Wykerd/modular-gps-tracker/Joernaal/21 April 2018.docx

21 April 2018

I visited Dr. Danie Ludick, who works at Stellenbosch University today to get expert advice on what capacitors and resistors to order. I also wanted him to check my design to confirm that it will work. He said that the design looks promising and that I should let it get manufactured, if it is to not work, he can help me solve the problem. He also said that he would send my design to his colleagues to also confirm that it will work. He also told me should I need help I can visit the University as they have all the tools I would need to make my PCB.

Below is a screenshot of the email I sent him:

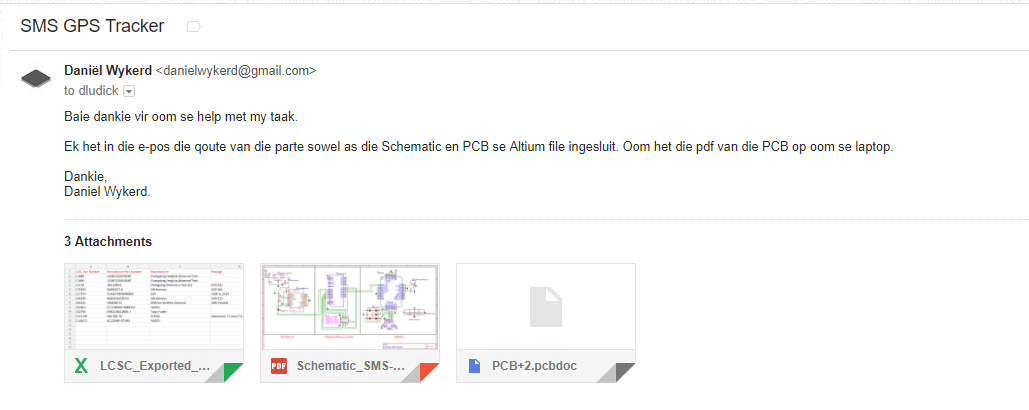
[picture p13: figure]
