Wykerd/modular-gps-tracker/Joernaal/28 april.docx

28 april

Started writing the research plan.

29 april

Made a case.

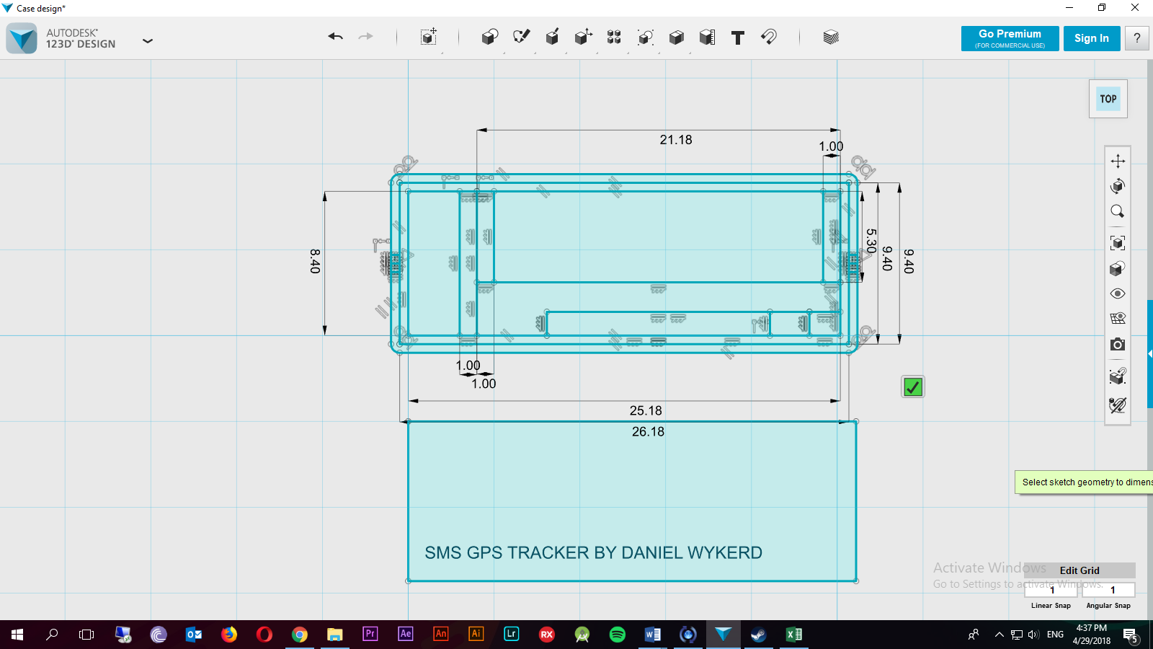
[picture p14: figure]
