Wykerd/modular-gps-tracker/Screenshots van code.docx

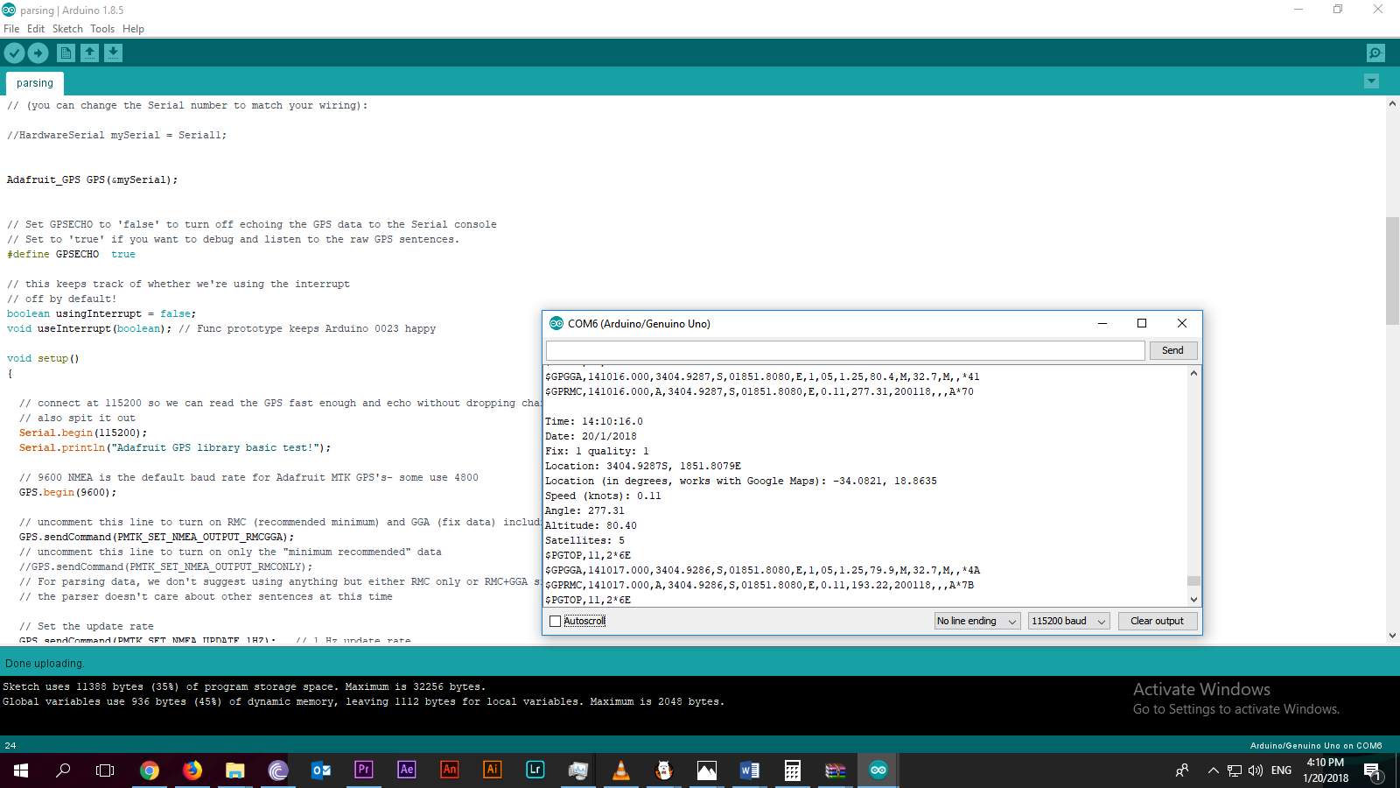
[picture p42: figure]

GPS test

1/20/2018
