Wykerd/modular-gps-tracker/Joernaal/22 April 2018.docx

22 April 2018

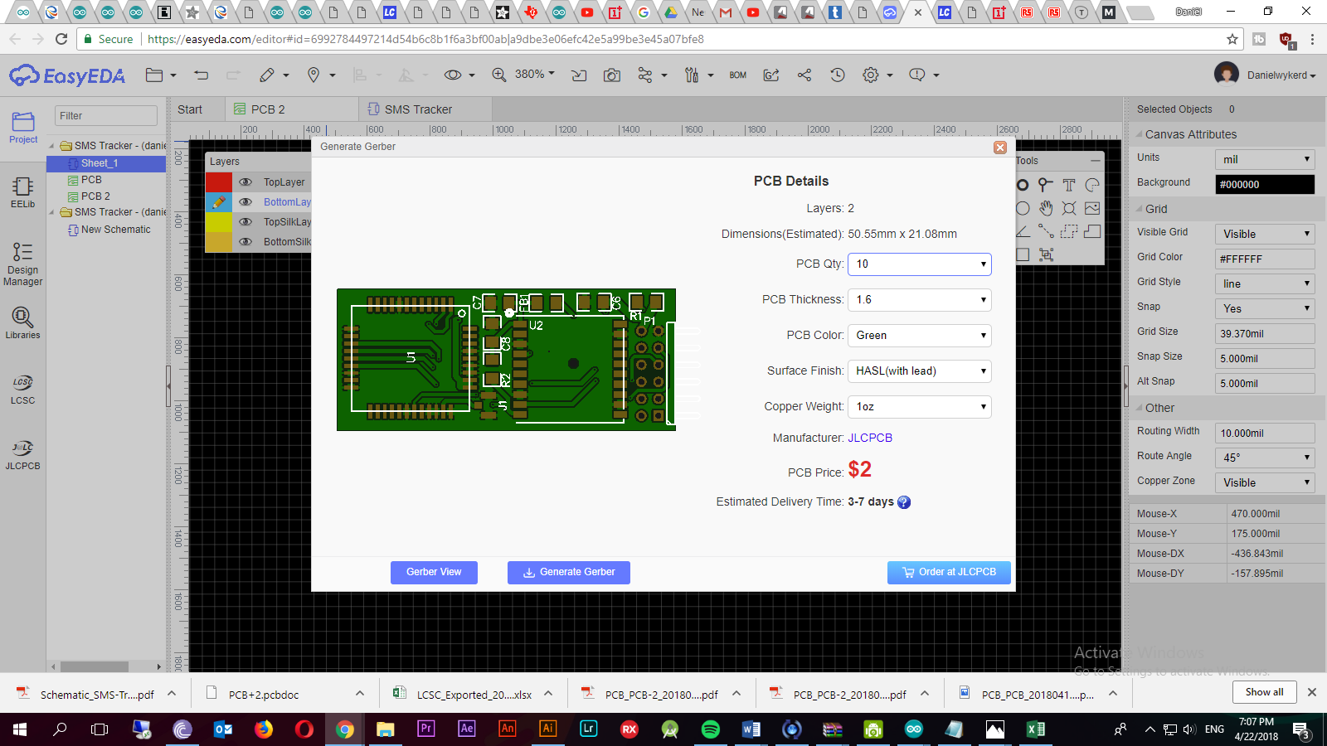
[picture p43: figure]
