Wykerd/modular-gps-tracker/Case bare.PNG

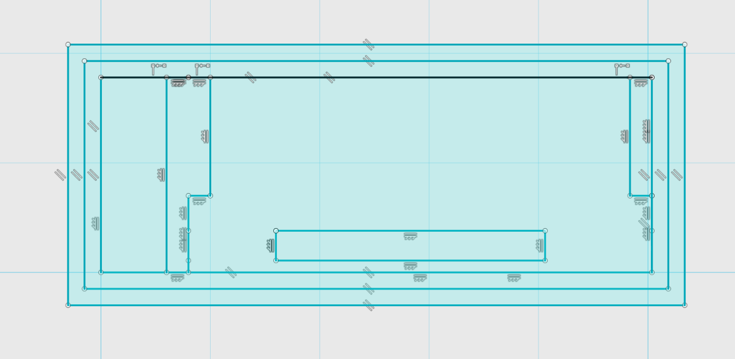
Case bare.PNG
