Wykerd/modular-gps-tracker/casedimensions.PNG

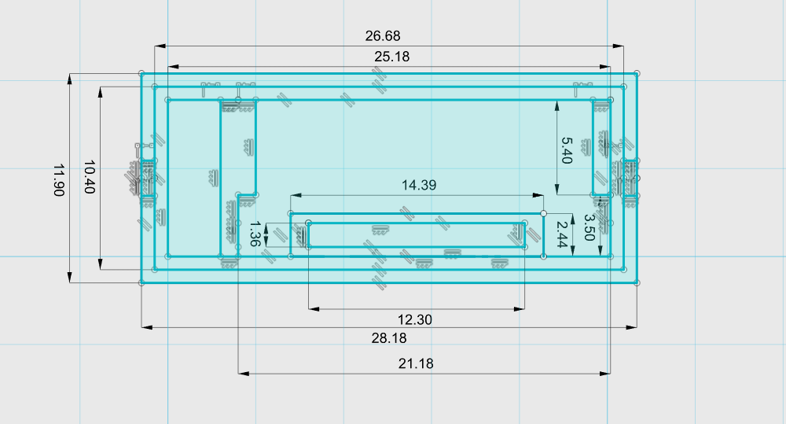
casedimensions.PNG
