Wykerd/modular-gps-tracker/Images/Hardware/20180120_152852.jpg

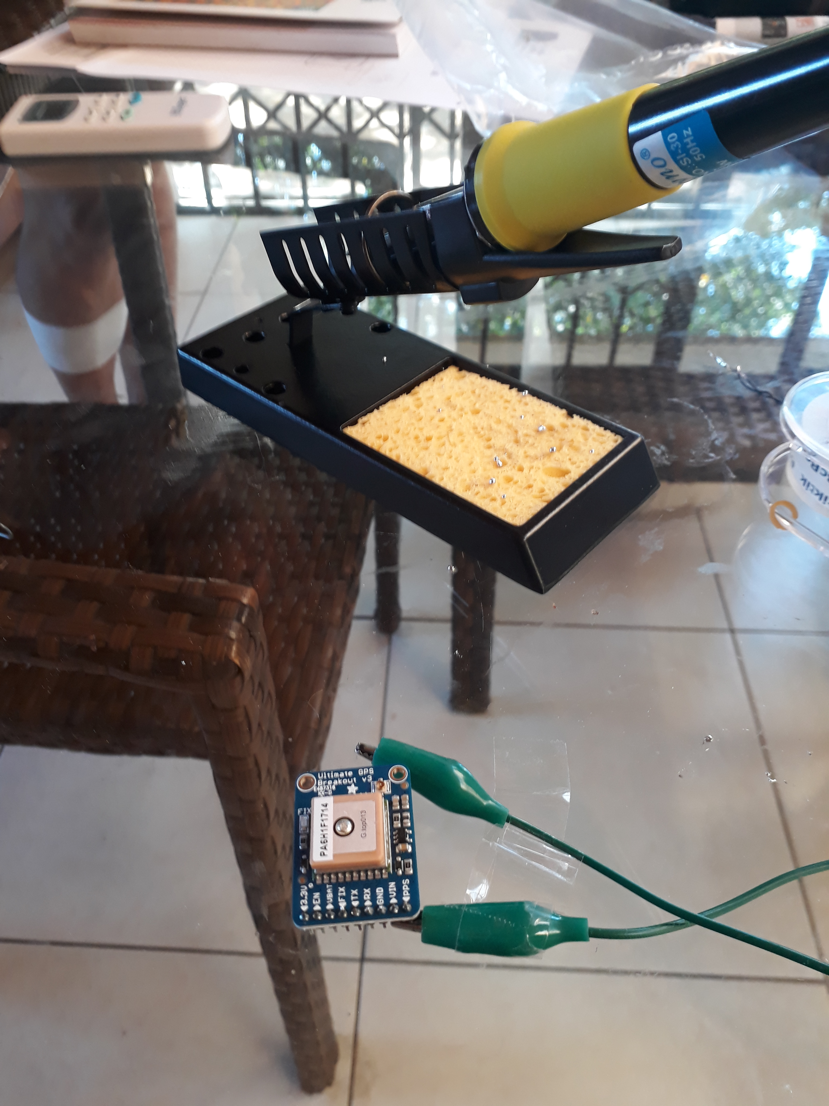
Images/Hardware/20180120_152852.jpg
