Wykerd/modular-gps-tracker/Images/Hardware/20180120_152857.jpg

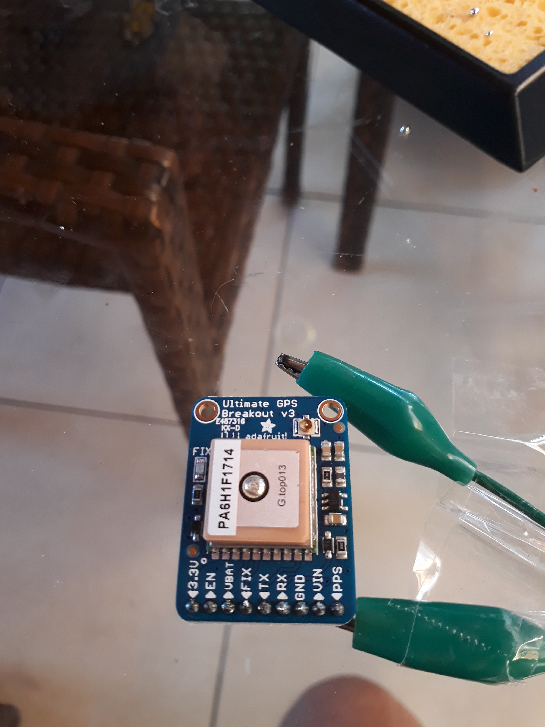
Images/Hardware/20180120_152857.jpg
