Wykerd/modular-gps-tracker/Images/Hardware/20180120_152902.jpg

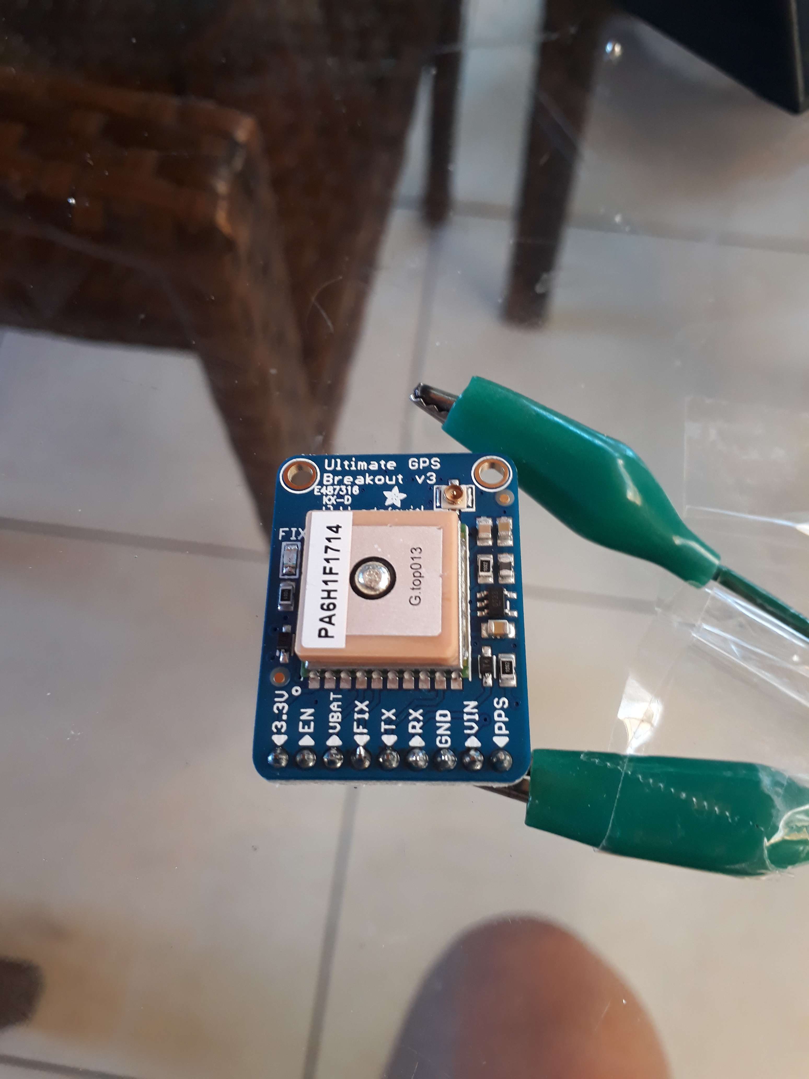
Images/Hardware/20180120_152902.jpg
