Wykerd/modular-gps-tracker/Images/Hardware/20180120_161100.jpg

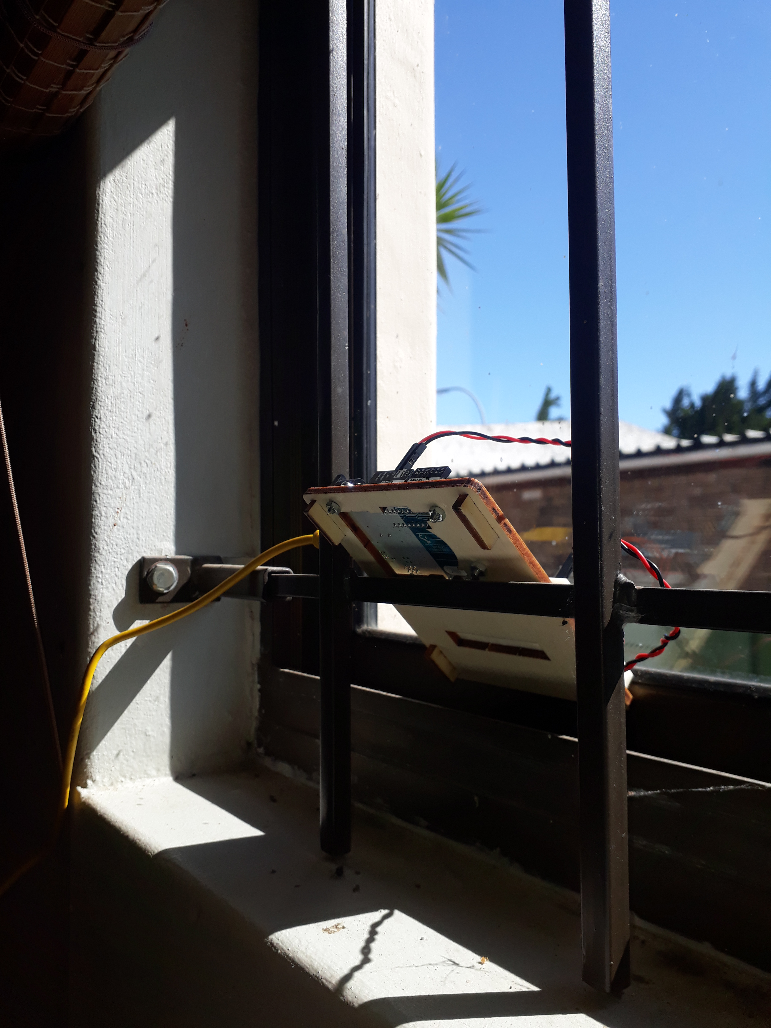
Images/Hardware/20180120_161100.jpg
