Wykerd/modular-gps-tracker/Images/Hardware/20180120_161110.jpg

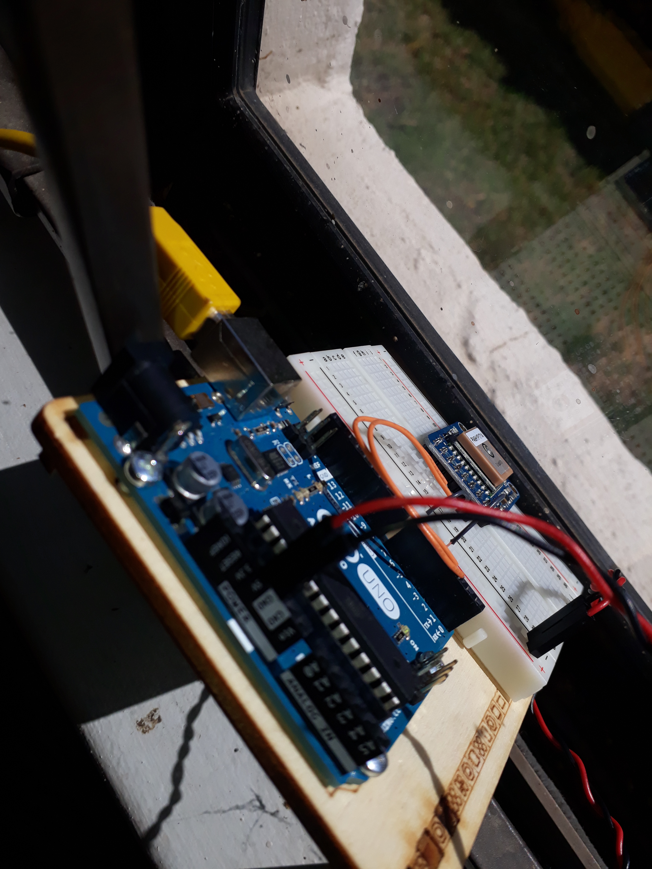
Images/Hardware/20180120_161110.jpg
