Wykerd/modular-gps-tracker/Images/Hardware/20180120_161119.jpg

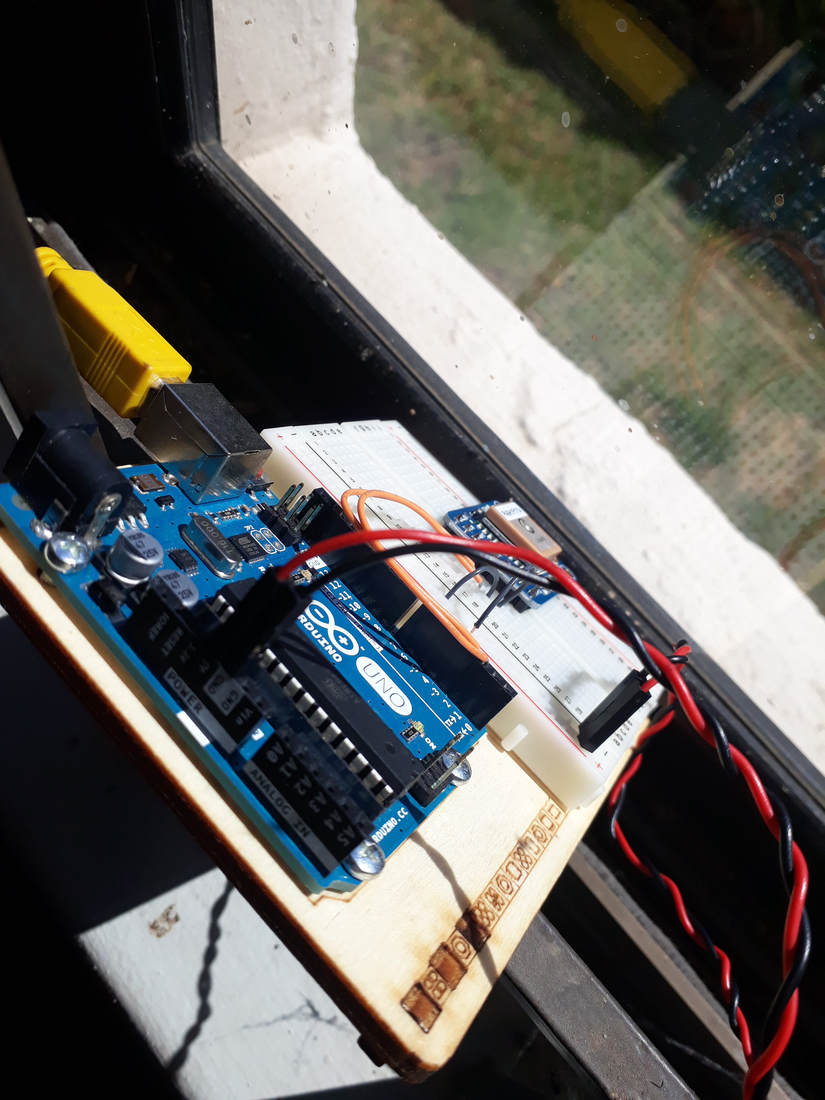
Images/Hardware/20180120_161119.jpg
