Wykerd/modular-gps-tracker/Images/Hardware/20180121_085342.jpg

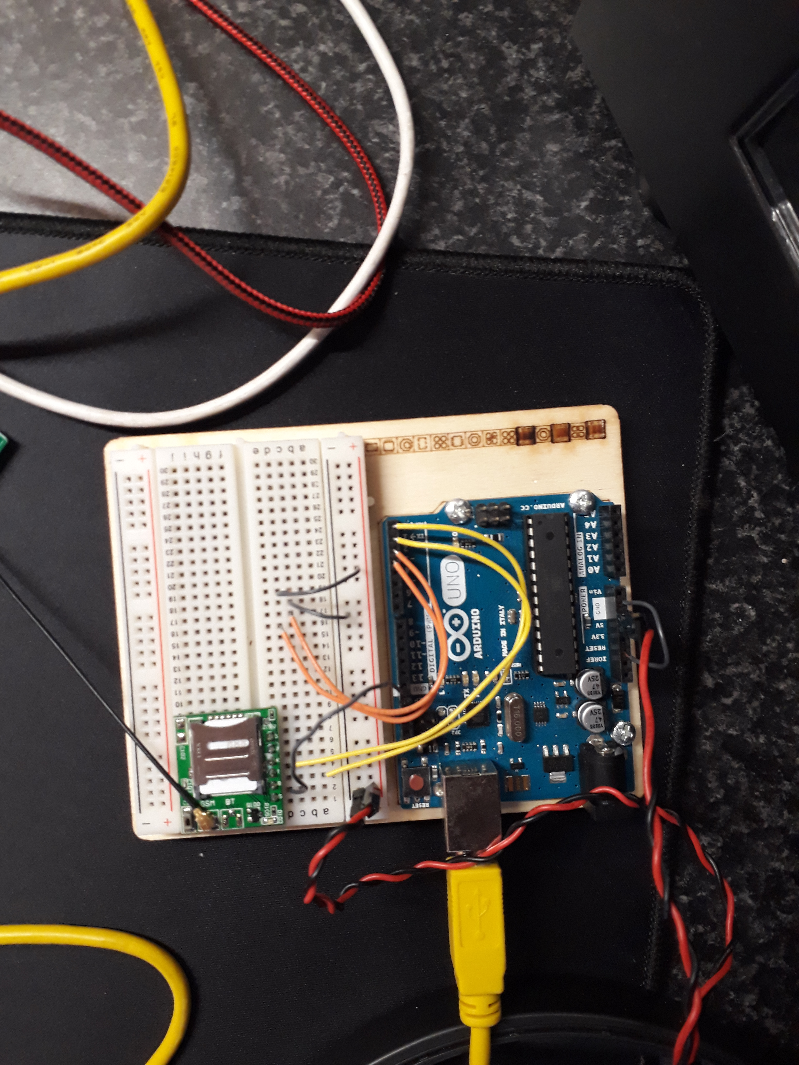
Images/Hardware/20180121_085342.jpg
