Wykerd/modular-gps-tracker/Images/Hardware/20180121_085343(0).jpg

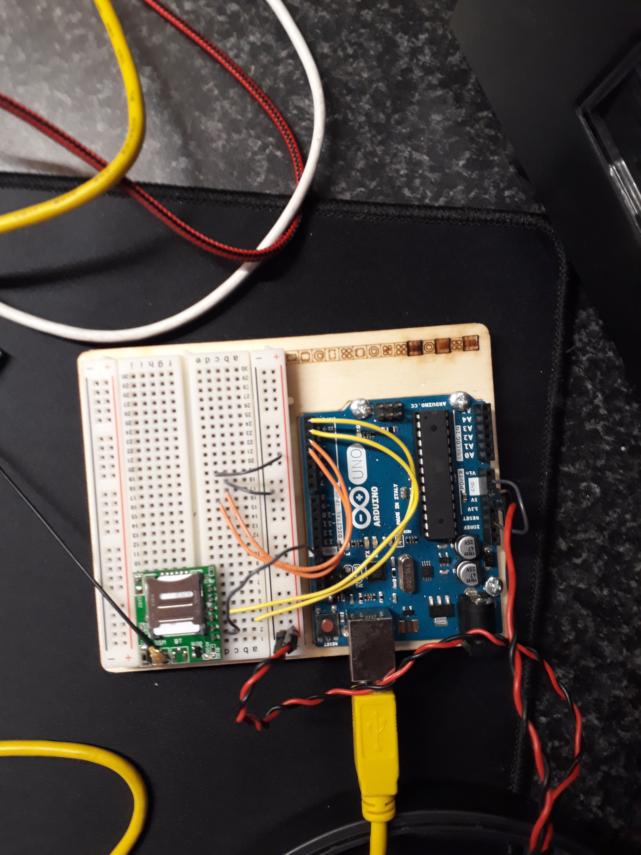
Images/Hardware/20180121_085343(0).jpg
