Wykerd/modular-gps-tracker/Images/Hardware/20180122_201225.jpg

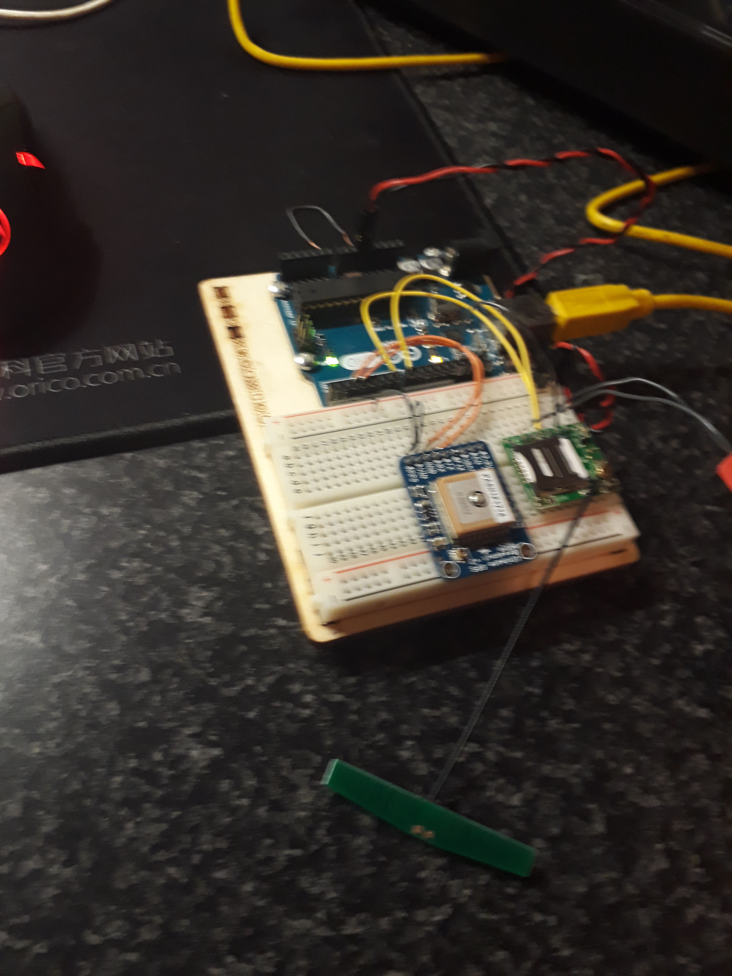
Images/Hardware/20180122_201225.jpg
