Wykerd/modular-gps-tracker/Images/Hardware/20180122_201243.jpg

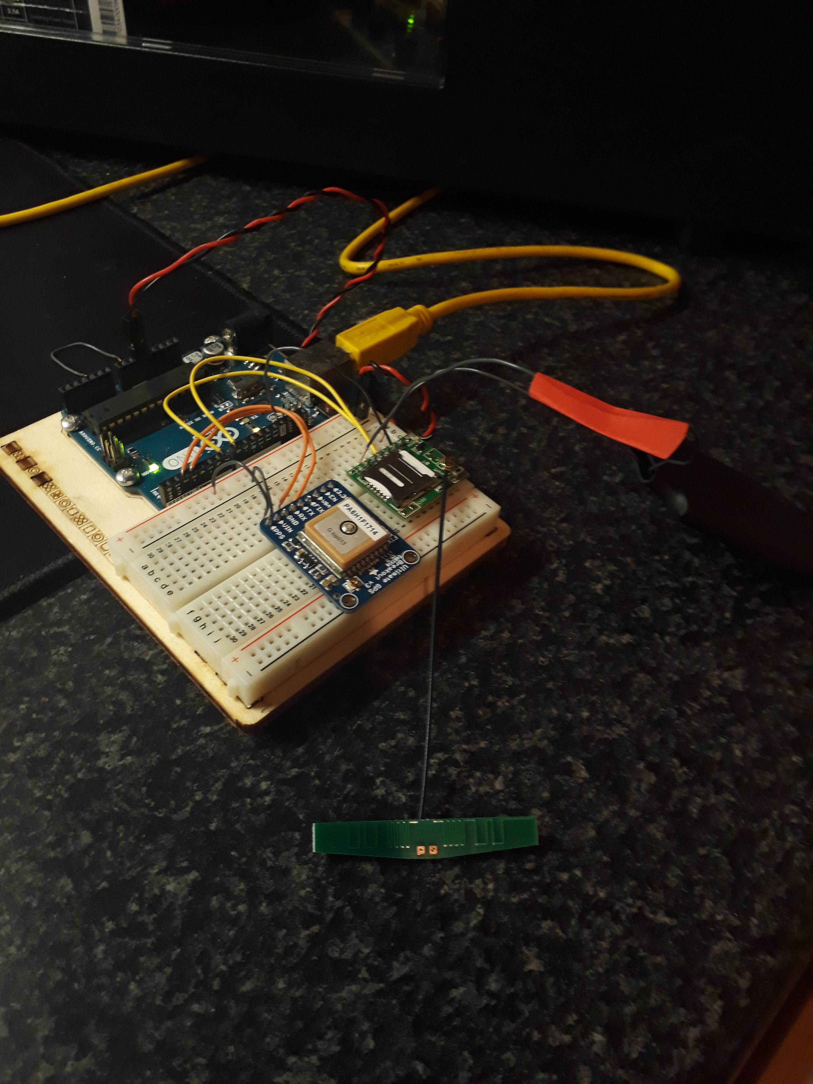
Images/Hardware/20180122_201243.jpg
