Wykerd/modular-gps-tracker/Images/Hardware/20180122_201249.jpg

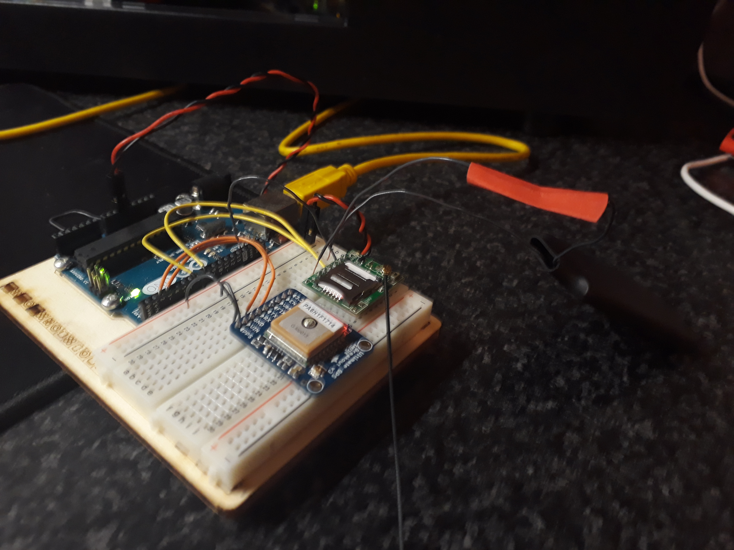
Images/Hardware/20180122_201249.jpg
