Wykerd/modular-gps-tracker/Images/Hardware/20180122_201251.jpg

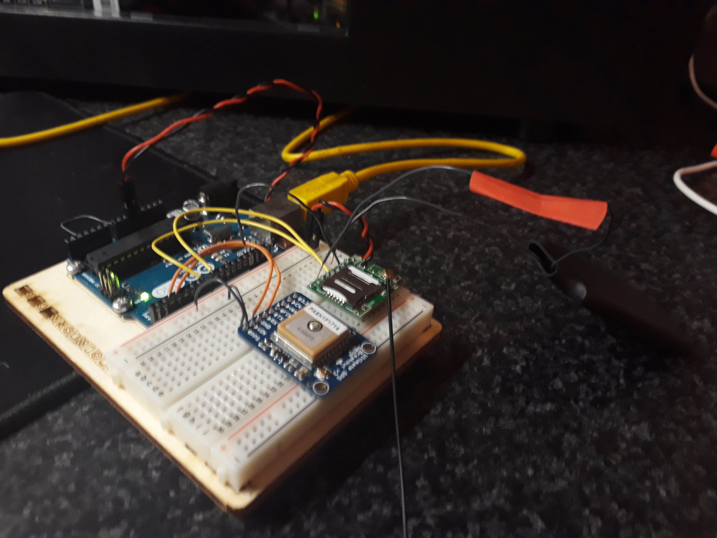
Images/Hardware/20180122_201251.jpg
