Wykerd/modular-gps-tracker/Images/Software/Screenshot_20180507-203700.png

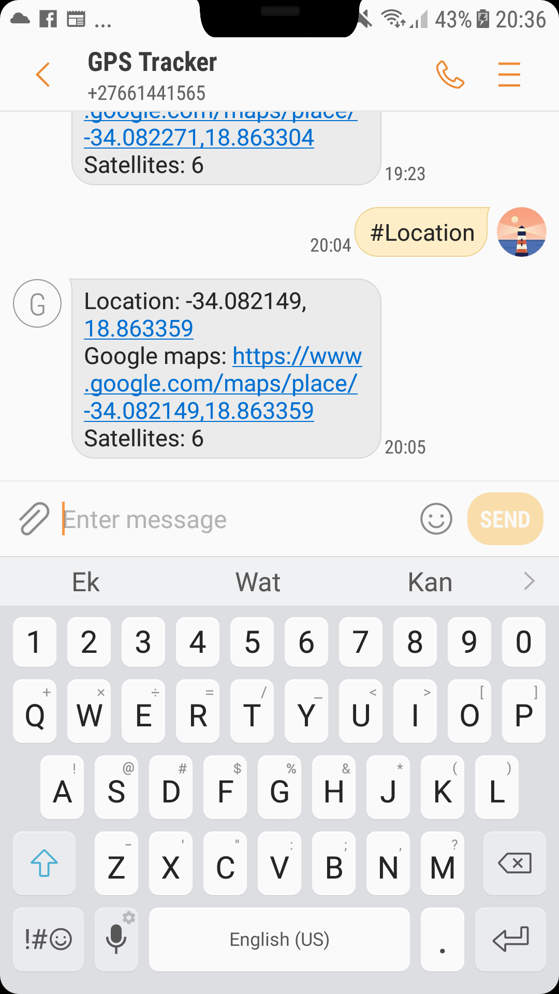
Images/Software/Screenshot_20180507-203700.png
