Wykerd/modular-gps-tracker/Images/Software/Screenshot_20180507-203848.png

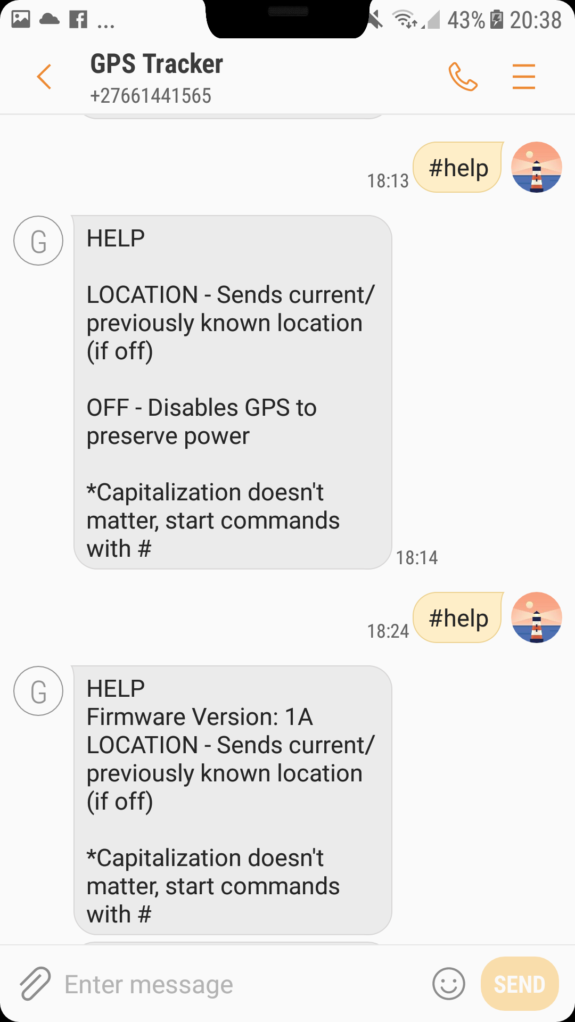
Images/Software/Screenshot_20180507-203848.png
