Wykerd/modular-gps-tracker/Nationals documents/Color Photo.jpeg

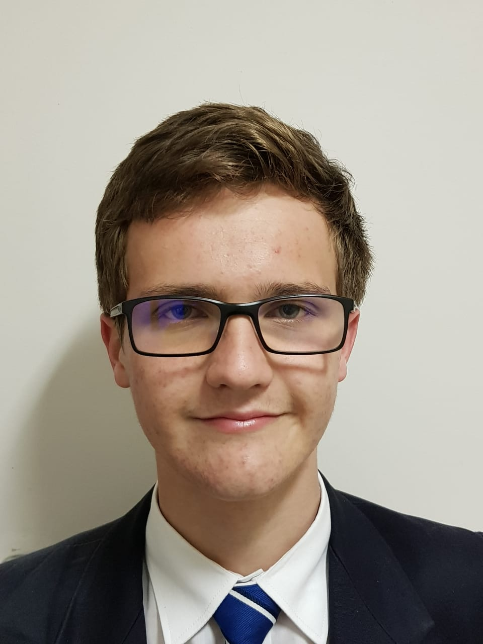
Nationals documents/Color Photo.jpeg
