Wykerd/modular-gps-tracker/Nationals documents/Report File Nationals/Images/FINAL/IMG_20180929_110307.jpg

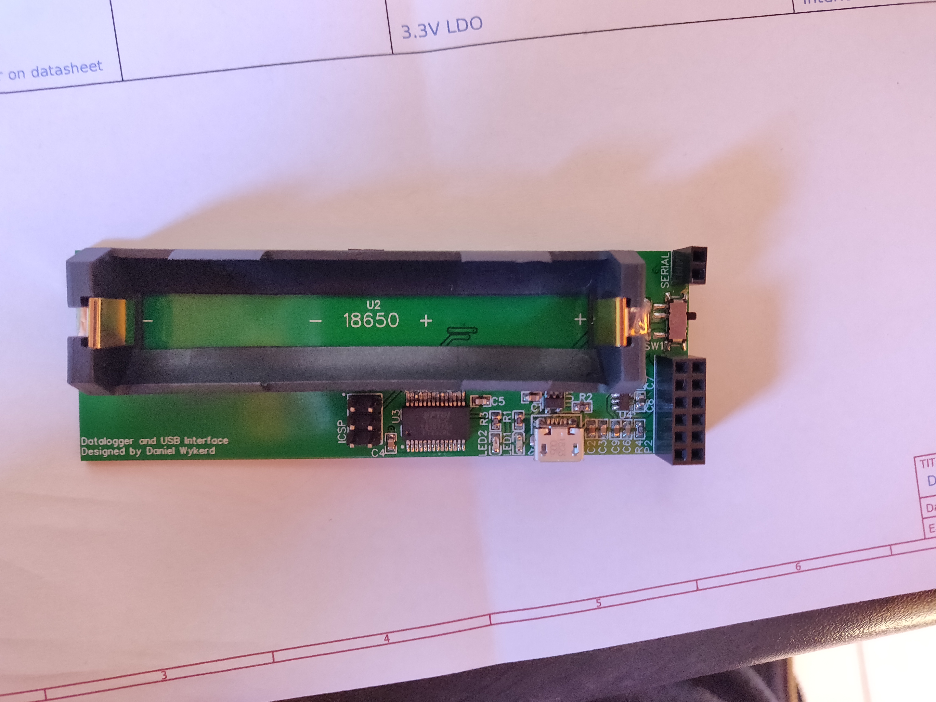
Nationals documents/Report File Nationals/Images/FINAL/IMG_20180929_110307.jpg
