Wykerd/modular-gps-tracker/Nationals documents/Report File Nationals/Schematics/FINAL DIAGRAM.png

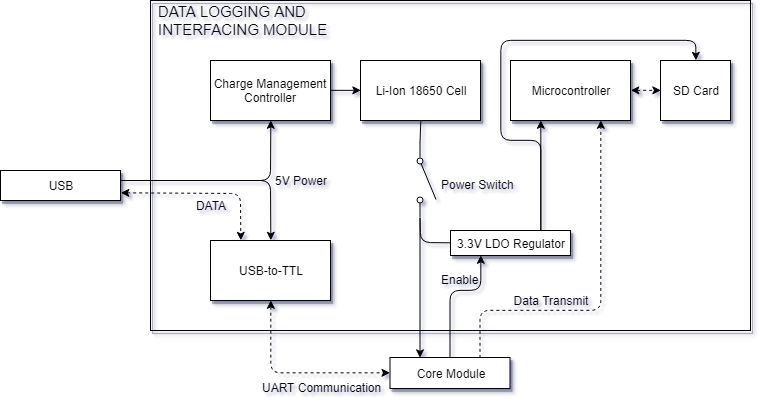
Nationals documents/Report File Nationals/Schematics/FINAL DIAGRAM.png
