Wykerd/modular-gps-tracker/Nationals documents/Report File Nationals/Schematics/PCB_PCB-1_20180925205440.png

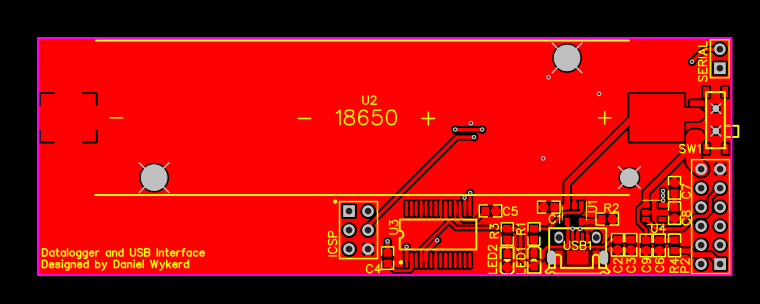
Nationals documents/Report File Nationals/Schematics/PCB_PCB-1_20180925205440.png
