Wykerd/modular-gps-tracker/Nationals documents/Report File Nationals/Schematics/PCB_PCB-1_20180925210639.png

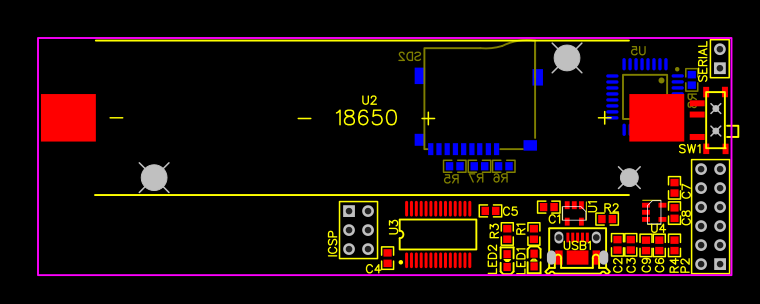
Nationals documents/Report File Nationals/Schematics/PCB_PCB-1_20180925210639.png
