Wykerd/modular-gps-tracker/Nationals documents/Report File Nationals/Schematics/Schematic_Bridge-module-battery-included_Sheet-1_20180925191030.png

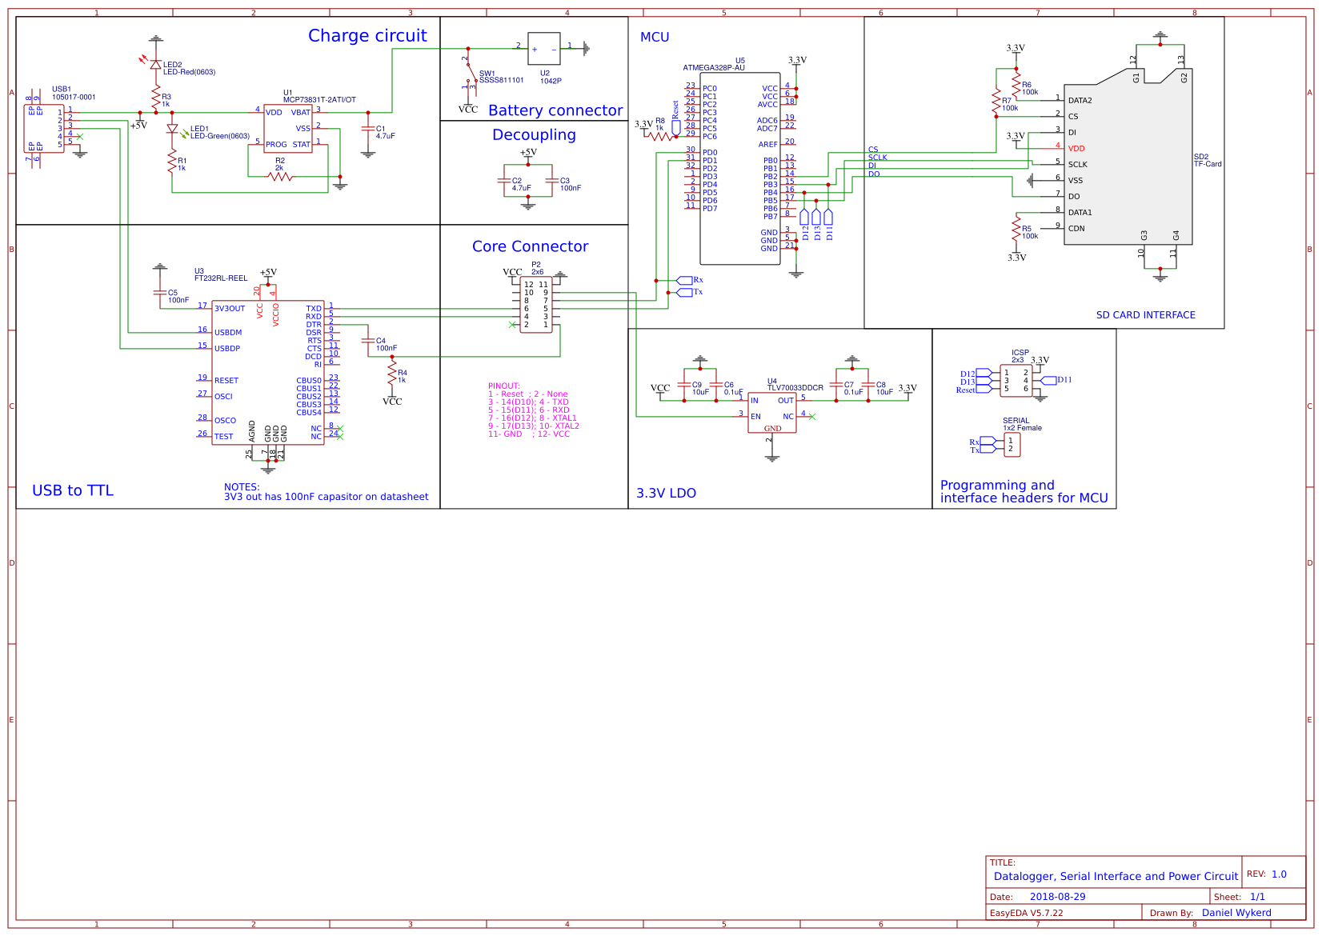
Nationals documents/Report File Nationals/Schematics/Schematic_Bridge-module-battery-included_Sheet-1_20180925191030.png
