Wykerd/modular-gps-tracker/Nationals documents/Report File Nationals/Schematics/Untitled Sketch_bb.png

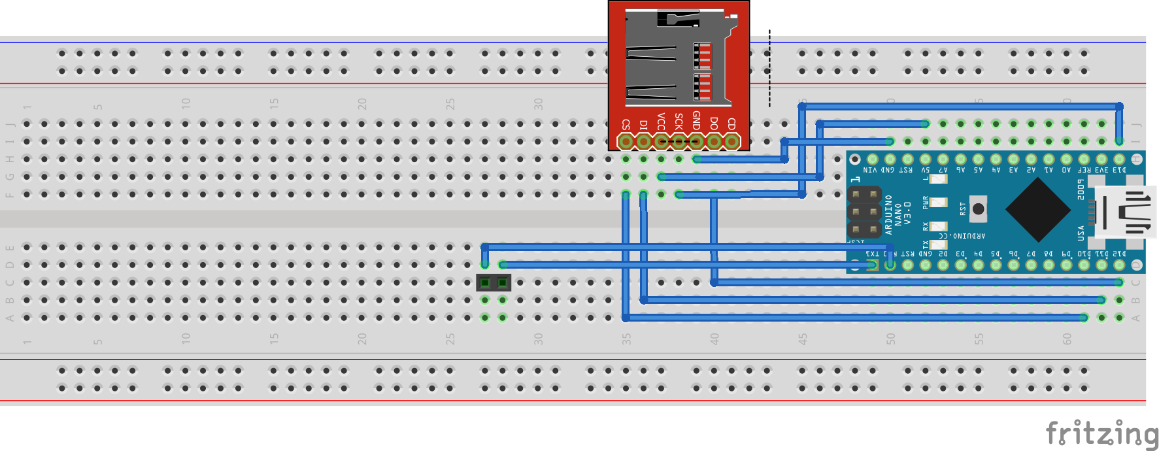
Nationals documents/Report File Nationals/Schematics/Untitled Sketch_bb.png
