Wykerd/modular-gps-tracker/Nationals documents/Report File Nationals/Schematics/Untitled Sketch_schem.png

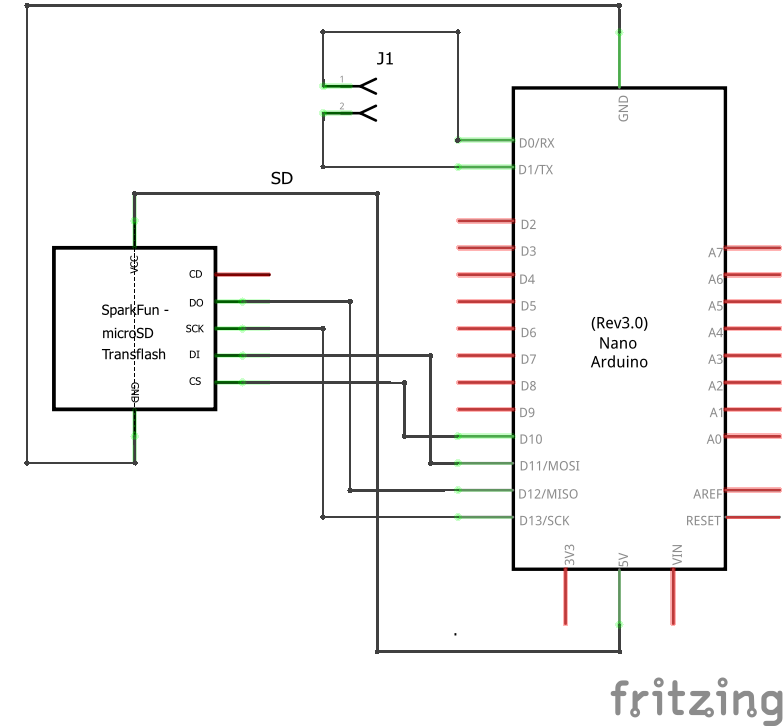
Nationals documents/Report File Nationals/Schematics/Untitled Sketch_schem.png
