Wykerd/modular-gps-tracker/Nationals documents/Report File Nationals/System diagram SD 1.png

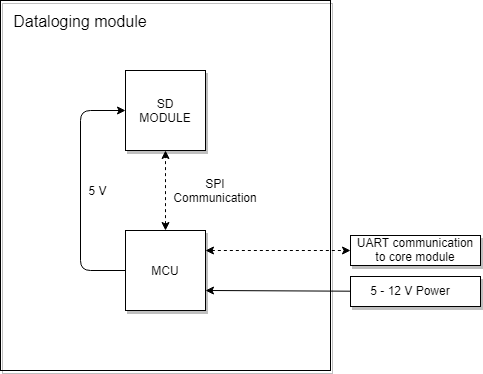
Nationals documents/Report File Nationals/System diagram SD 1.png
