Wykerd/modular-gps-tracker/PCB_PCB-2_20180508205844.png

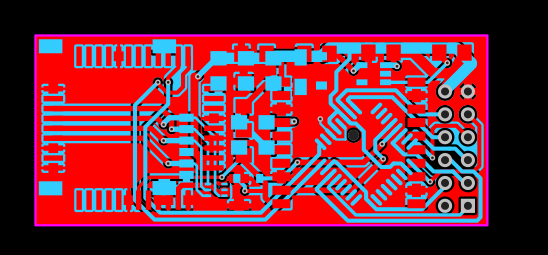
PCB_PCB-2_20180508205844.png
