Wykerd/modular-gps-tracker/PCB_PCB-2_20180508205912.png

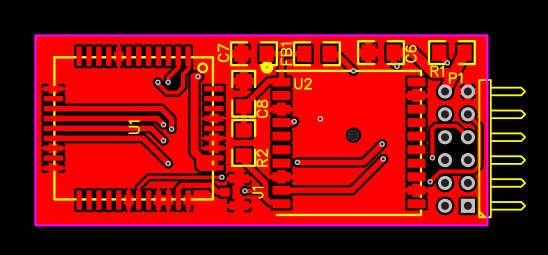
PCB_PCB-2_20180508205912.png
