Wykerd/modular-gps-tracker/PCB_PCB-2_20180508210208.png

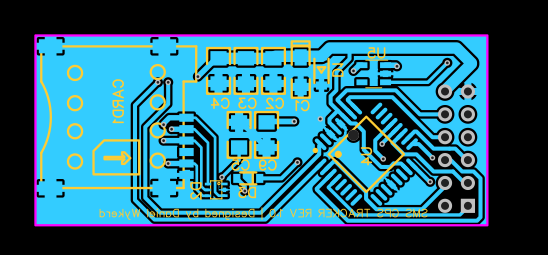
PCB_PCB-2_20180508210208.png
