Wykerd/modular-gps-tracker/PCB_PCB-2_20180508210503.png

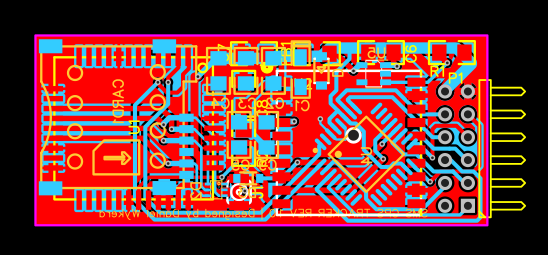
PCB_PCB-2_20180508210503.png
