Wykerd/modular-gps-tracker/PROTO-1-SYSTEM-DIAGRAM.png

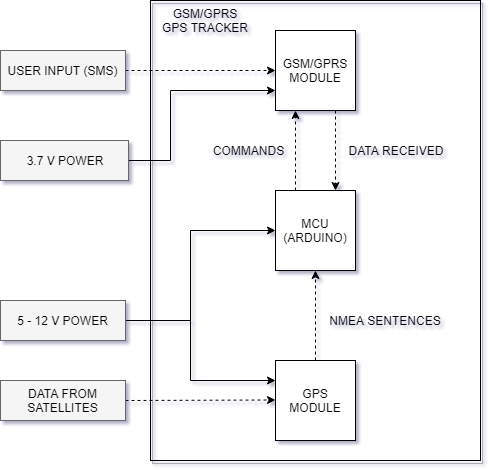
PROTO-1-SYSTEM-DIAGRAM.png
