Wykerd/modular-gps-tracker/PROTOTYPE 2 SCHEMATIC_bb.png

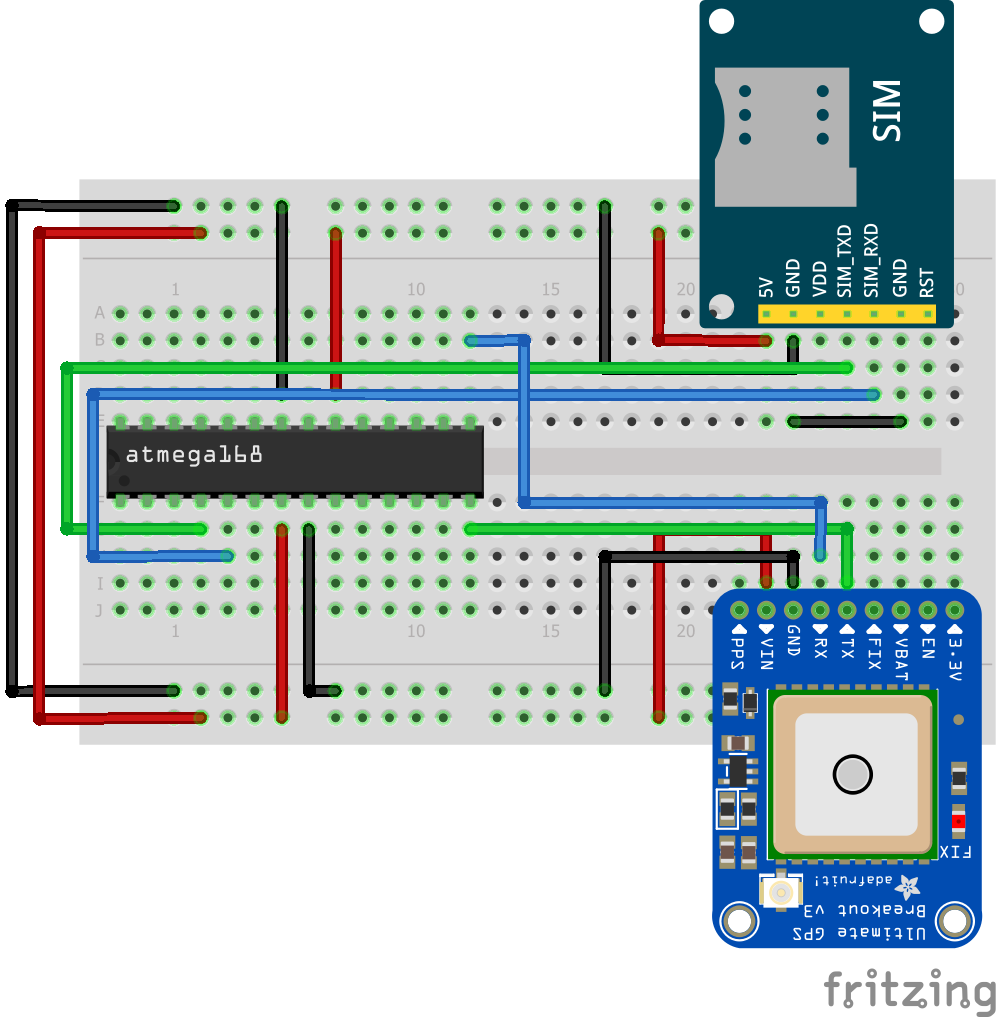
PROTOTYPE 2 SCHEMATIC_bb.png
