Wykerd/modular-gps-tracker/Schematic_SMS-Tracker_Sheet-1_20180415163453.png

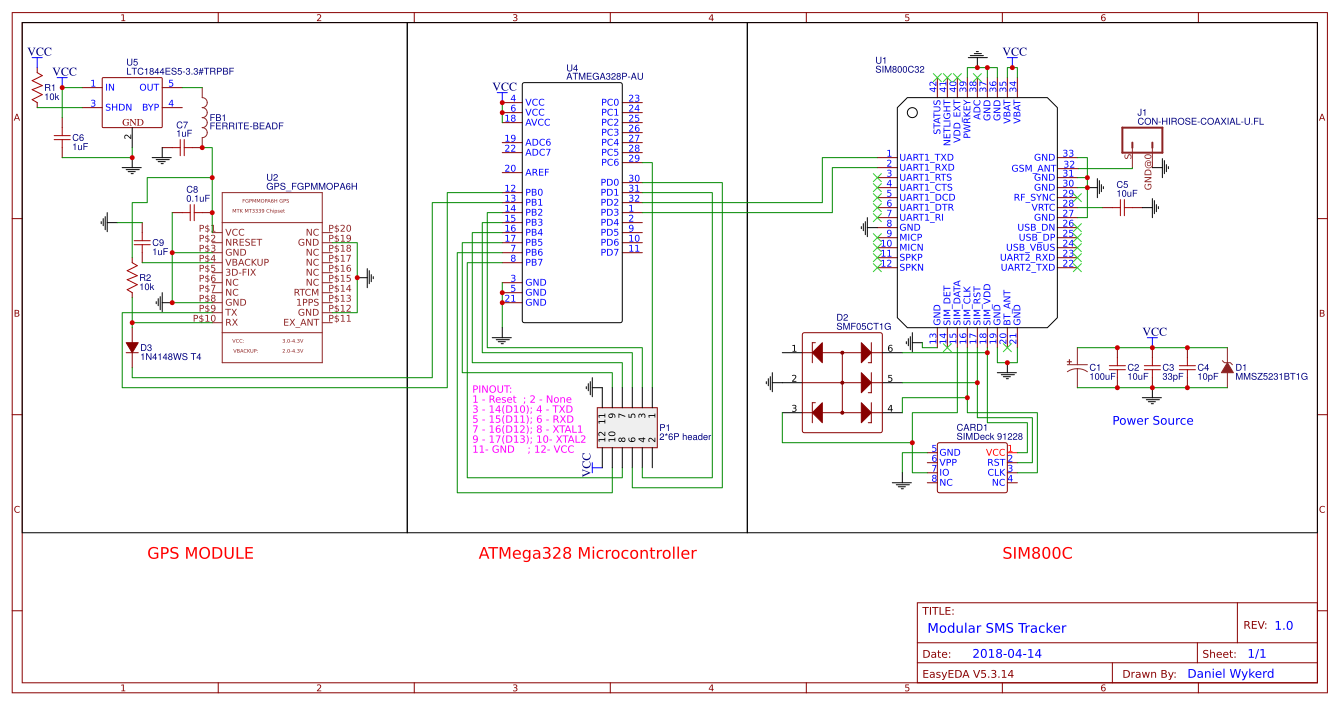
Schematic_SMS-Tracker_Sheet-1_20180415163453.png
