Wykerd/modular-gps-tracker/SMT_sizes.jpg

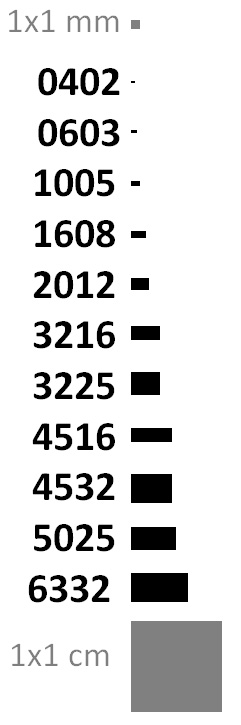
SMT_sizes.jpg
