Wykerd/modular-gps-tracker/Images/Hardware/20180120_152939.jpg

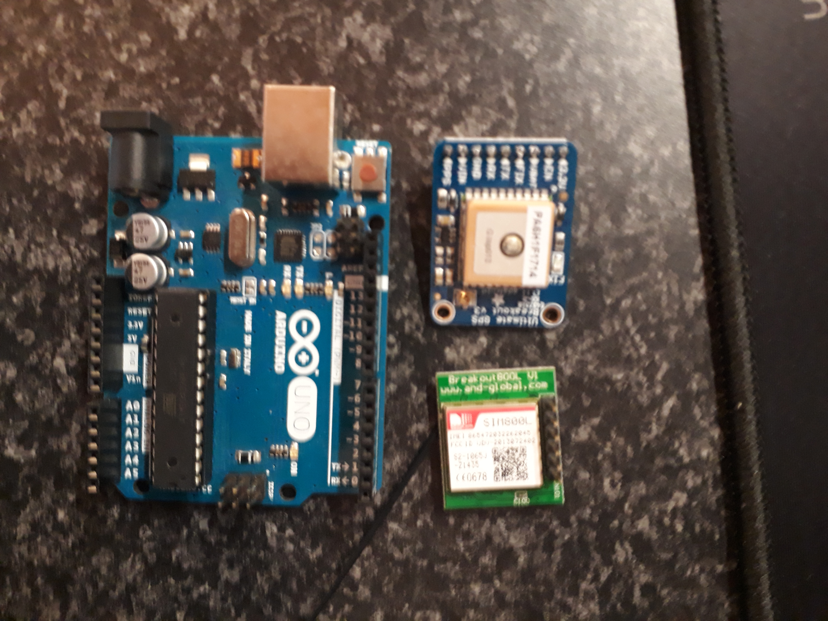
Images/Hardware/20180120_152939.jpg
