Wykerd/modular-gps-tracker/Images/Hardware/20180121_085326.jpg

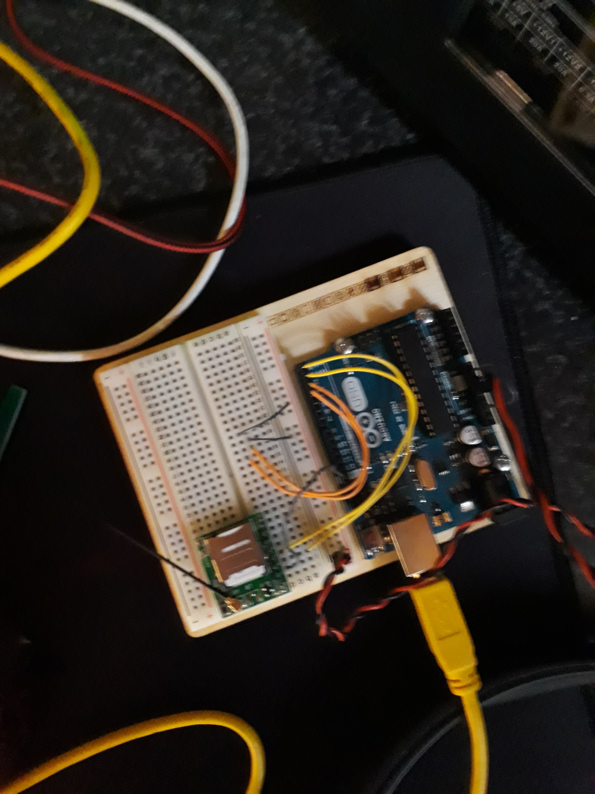
Images/Hardware/20180121_085326.jpg
