Wykerd/modular-gps-tracker/Images/Hardware/20180122_201241.jpg

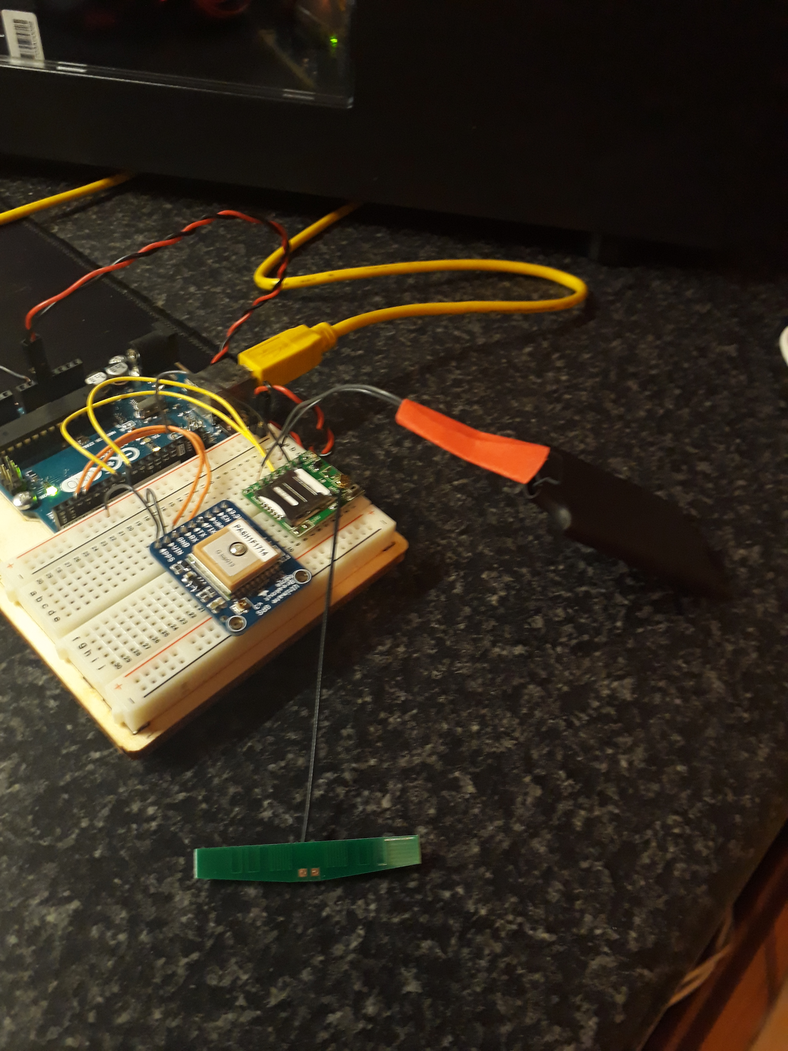
Images/Hardware/20180122_201241.jpg
