Wykerd/modular-gps-tracker/Images/Hardware/20180207_190835.jpg

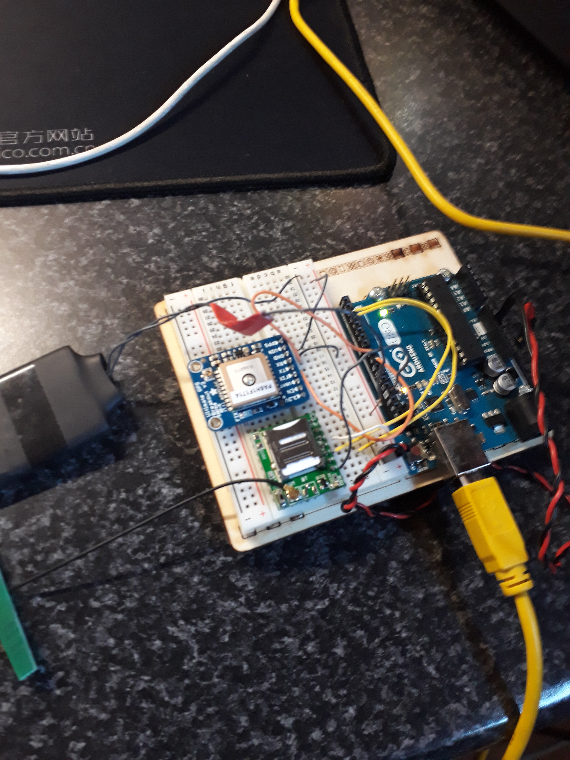
Images/Hardware/20180207_190835.jpg
