Wykerd/modular-gps-tracker/Images/Hardware/20180207_190841.jpg

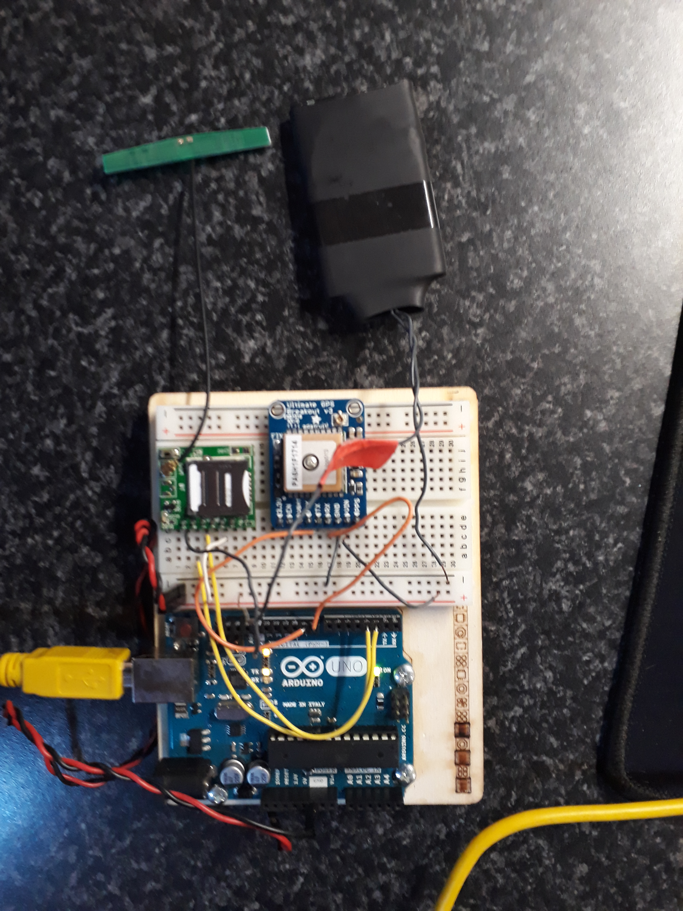
Images/Hardware/20180207_190841.jpg
