Wykerd/modular-gps-tracker/Images/Hardware/20180414_154636.jpg

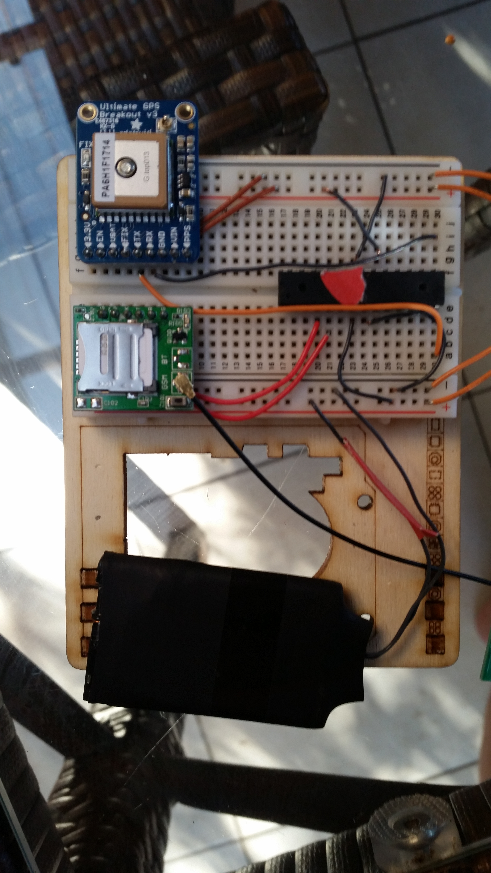
Images/Hardware/20180414_154636.jpg
