Wykerd/modular-gps-tracker/Images/Hardware/20180414_154641.jpg

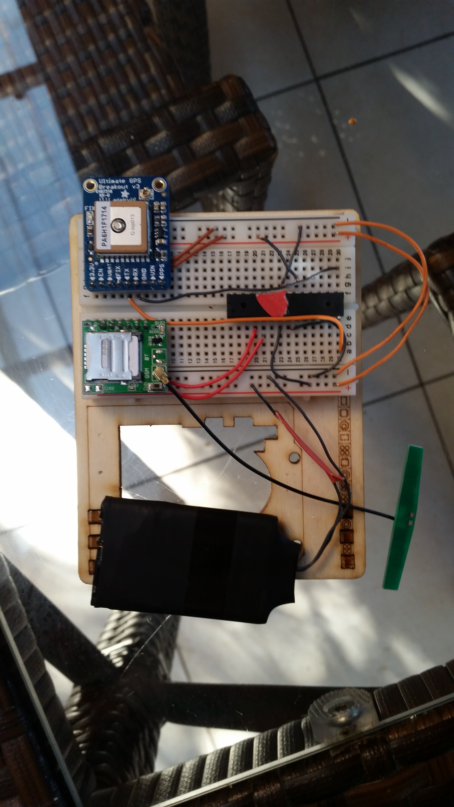
Images/Hardware/20180414_154641.jpg
