Wykerd/modular-gps-tracker/Nationals documents/Report File Nationals/Images/FINAL/IMG_20180929_104752.jpg

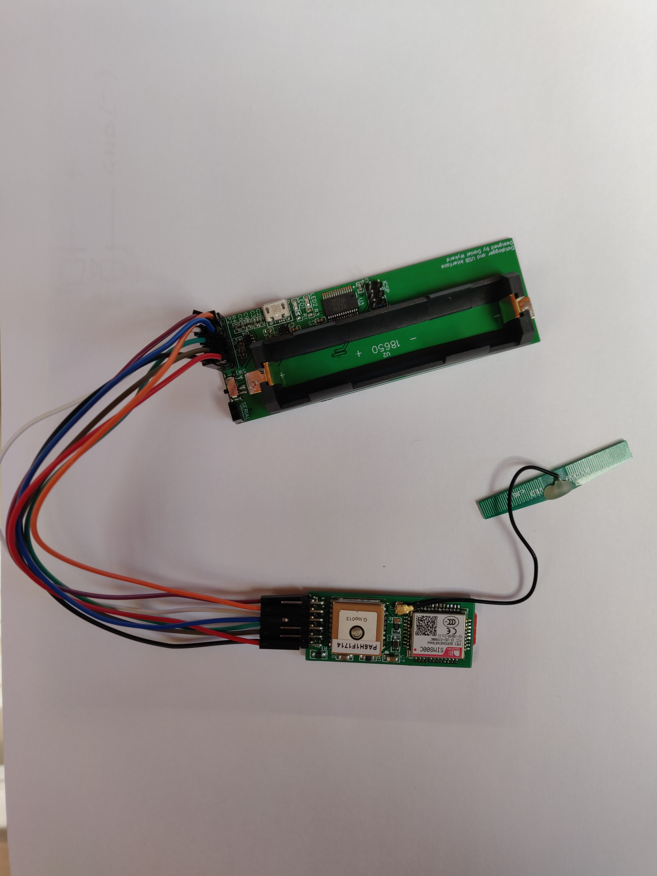
Nationals documents/Report File Nationals/Images/FINAL/IMG_20180929_104752.jpg
